keithmgould/beaker/schematics/main_schem.jpg

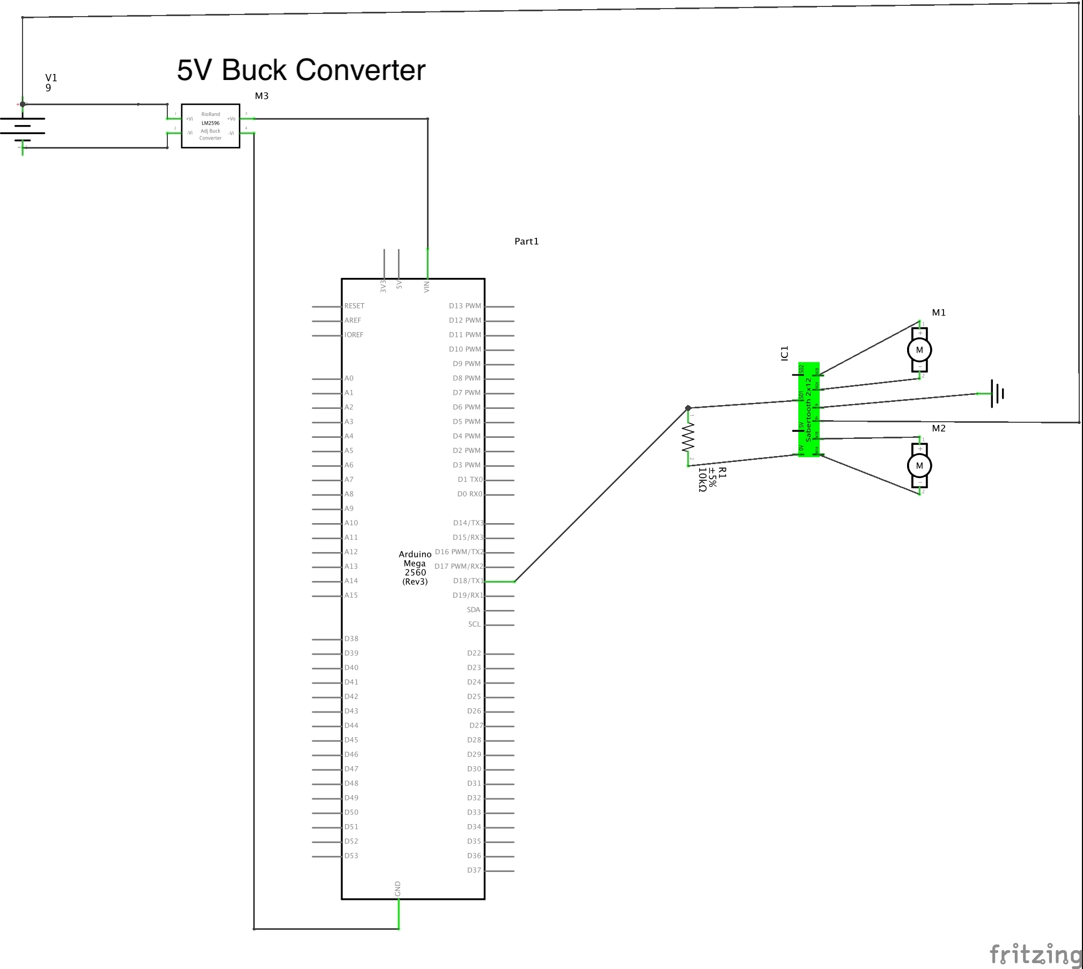
schematics/main_schem.jpg
