keithmgould/beaker/arduino/controllers/rPi_control/code/main.cpp

#include <Adafruit_Sensor.h>            // IMU
#include <Adafruit_BNO055.h>            // IMU
#include <Wire.h>                       // I2C for IMU
#include <EEPROM.h>
#include <StandardCplusplus.h>
#include <stdlib.h>
#include <string>
#include <sstream>                      // stringstream
#include "../../../lib/includes.h"     // common Beaker functionality

Imu my_imu;
Wheels wheels;
PiTalk piTalk(&Serial2);
Waiter outerWaiter(POSITION_CONTROL_TIMESTEP);
Waiter innerWaiter(MOTOR_CONTROL_TIMESTEP);
float outerDt = 0; // actual loop time of outer (slower) loop

bool shouldSendTelemetry = true;

void leftEncoderEvent(){ wheels.leftEncoderEvent(); }
void rightEncoderEvent(){ wheels.rightEncoderEvent(); }

// similar to buildTelemetry. Meant to stay small.
String buildState(){
  String state = String(my_imu.getTheta(),4) + "," + String(my_imu.getThetaDot(),4);
  state += "," + String(wheels.getX(),4) + "," + String(wheels.getPhiDotAvg(),4);
  return state;
}

// similar to buildState. Able to have more fields.
String buildTelemetry(){
  // outer loop time
  String log = String(outerDt);

  // raw states
  log += "," + String(my_imu.getTheta(),4) + "," + String(my_imu.getThetaDot(),4);
  log += "," + String(wheels.getX(),4) + "," + String(wheels.getPhiDotAvg(),4);

  // calibrations
  log += "," + String(my_imu.getThetaOffset(),4);

  // final result
  log += "," + String(wheels.getTargetRadsPerSec(),4);

  return log;
}

void sendTelemetry(){
  String log = buildTelemetry();
  Serial3.println(log);
}

void sendState(){
  String state = buildState();
  piTalk.sendToPi(state);
}

void toggleTelemetry(){
  shouldSendTelemetry = !shouldSendTelemetry;
  String response = "sending telemetry set to: " + String(shouldSendTelemetry);
  piTalk.sendToPi(response);
}

void showHelp(){
  String response = "S: send state.\n";
  response += "B: update Theta Offset.\n";                          // defined in pitalk.h
  response += "M: update Motor Pids.\n";                            // defined in pitalk.h
  response += "W: update to given rads/sec. ( No response )\n";     // defined in pitalk.h
  response += "A: accelerate by given rads/sec. ( No respons )\n";  // defined in pitalk.h
  response += "R: reset robot.\n";                                  // defined in pitalk.h
  response += "T: toggle telemetry. (It's currently "+ String(shouldSendTelemetry) +")\n";
  response += "H: this help.\n";

  piTalk.sendToPi(response);
}

void handlePiTalk(char command, std::string message){
  switch(command){
    case 'S': sendState(); break;
    case 'H': showHelp(); break;
    case 'T': toggleTelemetry(); break;
  }
}

void setup() {
  Serial3.begin(115200); while (!Serial3) {;} // bluetooth for telemetry
  piTalk.setup(&wheels, &my_imu, &handlePiTalk);
  my_imu.setup();
  attachInterrupt(digitalPinToInterrupt(LH_ENCODER_A), leftEncoderEvent, CHANGE);
  attachInterrupt(digitalPinToInterrupt(RH_ENCODER_A), rightEncoderEvent, CHANGE);
  wheels.initialize();
  Outputs::init();
}

void loop(){
  // inner loop behavior
  if(innerWaiter.isTime()){
    float innerDt = innerWaiter.starting();
    wheels.spin(innerDt);
    my_imu.pushThetaDotData();
    piTalk.checkForResponse();
  }

  // outer loop behavior
  if(outerWaiter.isTime()){
    outerDt = outerWaiter.starting();
    my_imu.update();

    if(shouldSendTelemetry) { sendTelemetry(); }
    piTalk.sendToPi(buildState());
  }
}
