keithmgould/beaker/raspberry_pi/neural_networks/reinforcement_learning/ddpg2.py

"""
Implementation of DDPG - Deep Deterministic Policy Gradient

Algorithm and hyperparameter details can be found here:
    http://arxiv.org/pdf/1509.02971v2.pdf

The algorithm is tested on the Pendulum-v0 OpenAI gym task
and developed with tflearn + Tensorflow

Author: Patrick Emami
"""
import tensorflow as tf
import numpy as np
import tflearn
import argparse
import pprint as pp

import RPi.GPIO as GPIO # for reset button
from lib.world import World

import time
import pdb

# ===========================
#   Actor and Critic DNNs
# ===========================

class ActorNetwork(object):
    """
    Input to the network is the state, output is the action
    under a deterministic policy.

    The output layer activation is a tanh to keep the action
    between -action_bound and action_bound
    """

    def __init__(self, sess, state_dim, action_dim, action_bound, learning_rate, tau, batch_size):
        self.sess = sess
        self.s_dim = state_dim
        self.a_dim = action_dim
        self.action_bound = action_bound
        self.learning_rate = learning_rate
        self.tau = tau
        self.batch_size = batch_size

        # Actor Network
        self.inputs, self.out, self.scaled_out = self.create_actor_network()

        self.network_params = tf.trainable_variables()

        # Target Network
        self.target_inputs, self.target_out, self.target_scaled_out = self.create_actor_network()

        self.target_network_params = tf.trainable_variables()[
            len(self.network_params):]

        # Op for periodically updating target network with online network
        # weights
        self.update_target_network_params = \
            [self.target_network_params[i].assign(tf.multiply(self.network_params[i], self.tau) +
                                                  tf.multiply(self.target_network_params[i], 1. - self.tau))
                for i in range(len(self.target_network_params))]

        # This gradient will be provided by the critic network
        self.action_gradient = tf.placeholder(tf.float32, [None, self.a_dim])

        # Combine the gradients here
        self.unnormalized_actor_gradients = tf.gradients(
            self.scaled_out, self.network_params, -self.action_gradient)
        self.actor_gradients = list(map(lambda x: tf.div(x, self.batch_size), self.unnormalized_actor_gradients))

        # Optimization Op
        self.optimize = tf.train.AdamOptimizer(self.learning_rate).\
            apply_gradients(zip(self.actor_gradients, self.network_params))

        self.num_trainable_vars = len(
            self.network_params) + len(self.target_network_params)

    def create_actor_network(self):
        inputs = tflearn.input_data(shape=[None, self.s_dim])
        net = tflearn.fully_connected(inputs, 400)
        net = tflearn.layers.normalization.batch_normalization(net)
        net = tflearn.activations.relu(net)
        net = tflearn.fully_connected(net, 300)
        net = tflearn.layers.normalization.batch_normalization(net)
        net = tflearn.activations.relu(net)
        # Final layer weights are init to Uniform[-3e-3, 3e-3]
        w_init = tflearn.initializations.uniform(minval=-0.003, maxval=0.003)
        out = tflearn.fully_connected(
            net, self.a_dim, activation='tanh', weights_init=w_init)
        # Scale output to -action_bound to action_bound
        scaled_out = tf.multiply(out, self.action_bound)
        return inputs, out, scaled_out

    def predict(self, inputs):
        return self.sess.run(self.scaled_out, feed_dict={
            self.inputs: inputs
        })

    def predict_target(self, inputs):
        return self.sess.run(self.target_scaled_out, feed_dict={
            self.target_inputs: inputs
        })

    def update_target_network(self):
        self.sess.run(self.update_target_network_params)

    def get_num_trainable_vars(self):
        return self.num_trainable_vars


def main(args):

    with tf.Session() as sess:
        env = World()
        
        np.random.seed(int(args['random_seed']))
        tf.set_random_seed(int(args['random_seed']))
        

        state_dim = env.observation_space.shape[0]
        action_dim = env.action_space.shape[0]
        action_bound = env.action_space.high
        # Ensure action bound is symmetric

        assert (env.action_space.high == -env.action_space.low)

        actor = ActorNetwork(sess, state_dim, action_dim, action_bound,
                             float(args['actor_lr']), float(args['tau']),
                             int(args['minibatch_size']))


        saver = tf.train.Saver(max_to_keep=5)
        latest_checkpoint = tf.train.latest_checkpoint('./models/ddpg/')
        saver.restore(sess, latest_checkpoint)

        while(True):
            observation, reward, done = env.reset(), 0, False
            throw_away_action = actor.predict([observation]) # prime network.

            while(True):
                action = actor.predict([observation])
                observation, reward, done = env.step(action)
                if observation == False: # some sort of error communicating w Arduino
                  done = False # prob not needed (already false) but just to be safe
                  break # lets try another rollout
                if done:
                  break


if __name__ == '__main__':
    parser = argparse.ArgumentParser(description='provide arguments for DDPG agent')

    # agent parameters
    parser.add_argument('--actor-lr', help='actor network learning rate', default=0.0001)
    parser.add_argument('--tau', help='soft target update parameter', default=0.001)
    parser.add_argument('--random-seed', help='random seed for repeatability', default=1234)
    parser.add_argument('--minibatch-size', help='size of minibatch for minibatch-SGD', default=64)


    # run parameters
    
    parser.add_argument('--max-episode-len', help='max length of 1 episode', default=1000)
    
    args = vars(parser.parse_args())

    pp.pprint(args)

    main(args)
